calvin-mcd/lumpen/Images/image-1.png

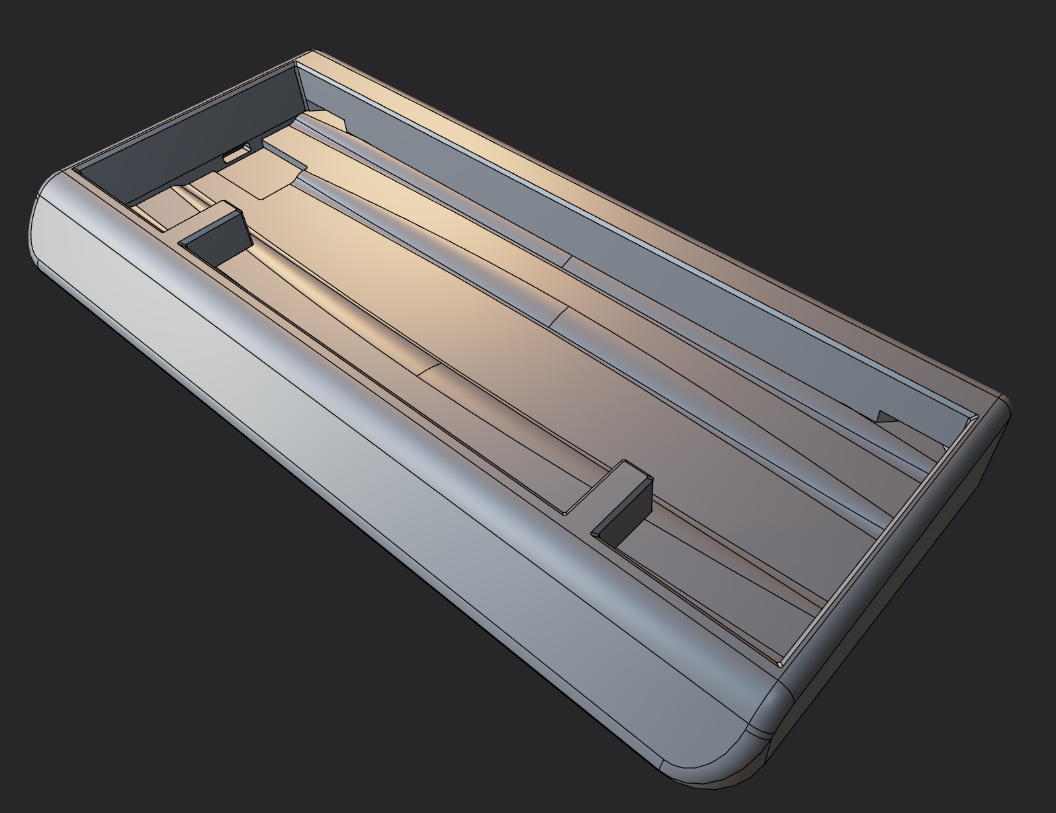
Images/image-1.png
