calvin-mcd/lumpen/Project/lumpen.kicad_sch

## KiCad design Project/lumpen.kicad_sch (2023-02-24)

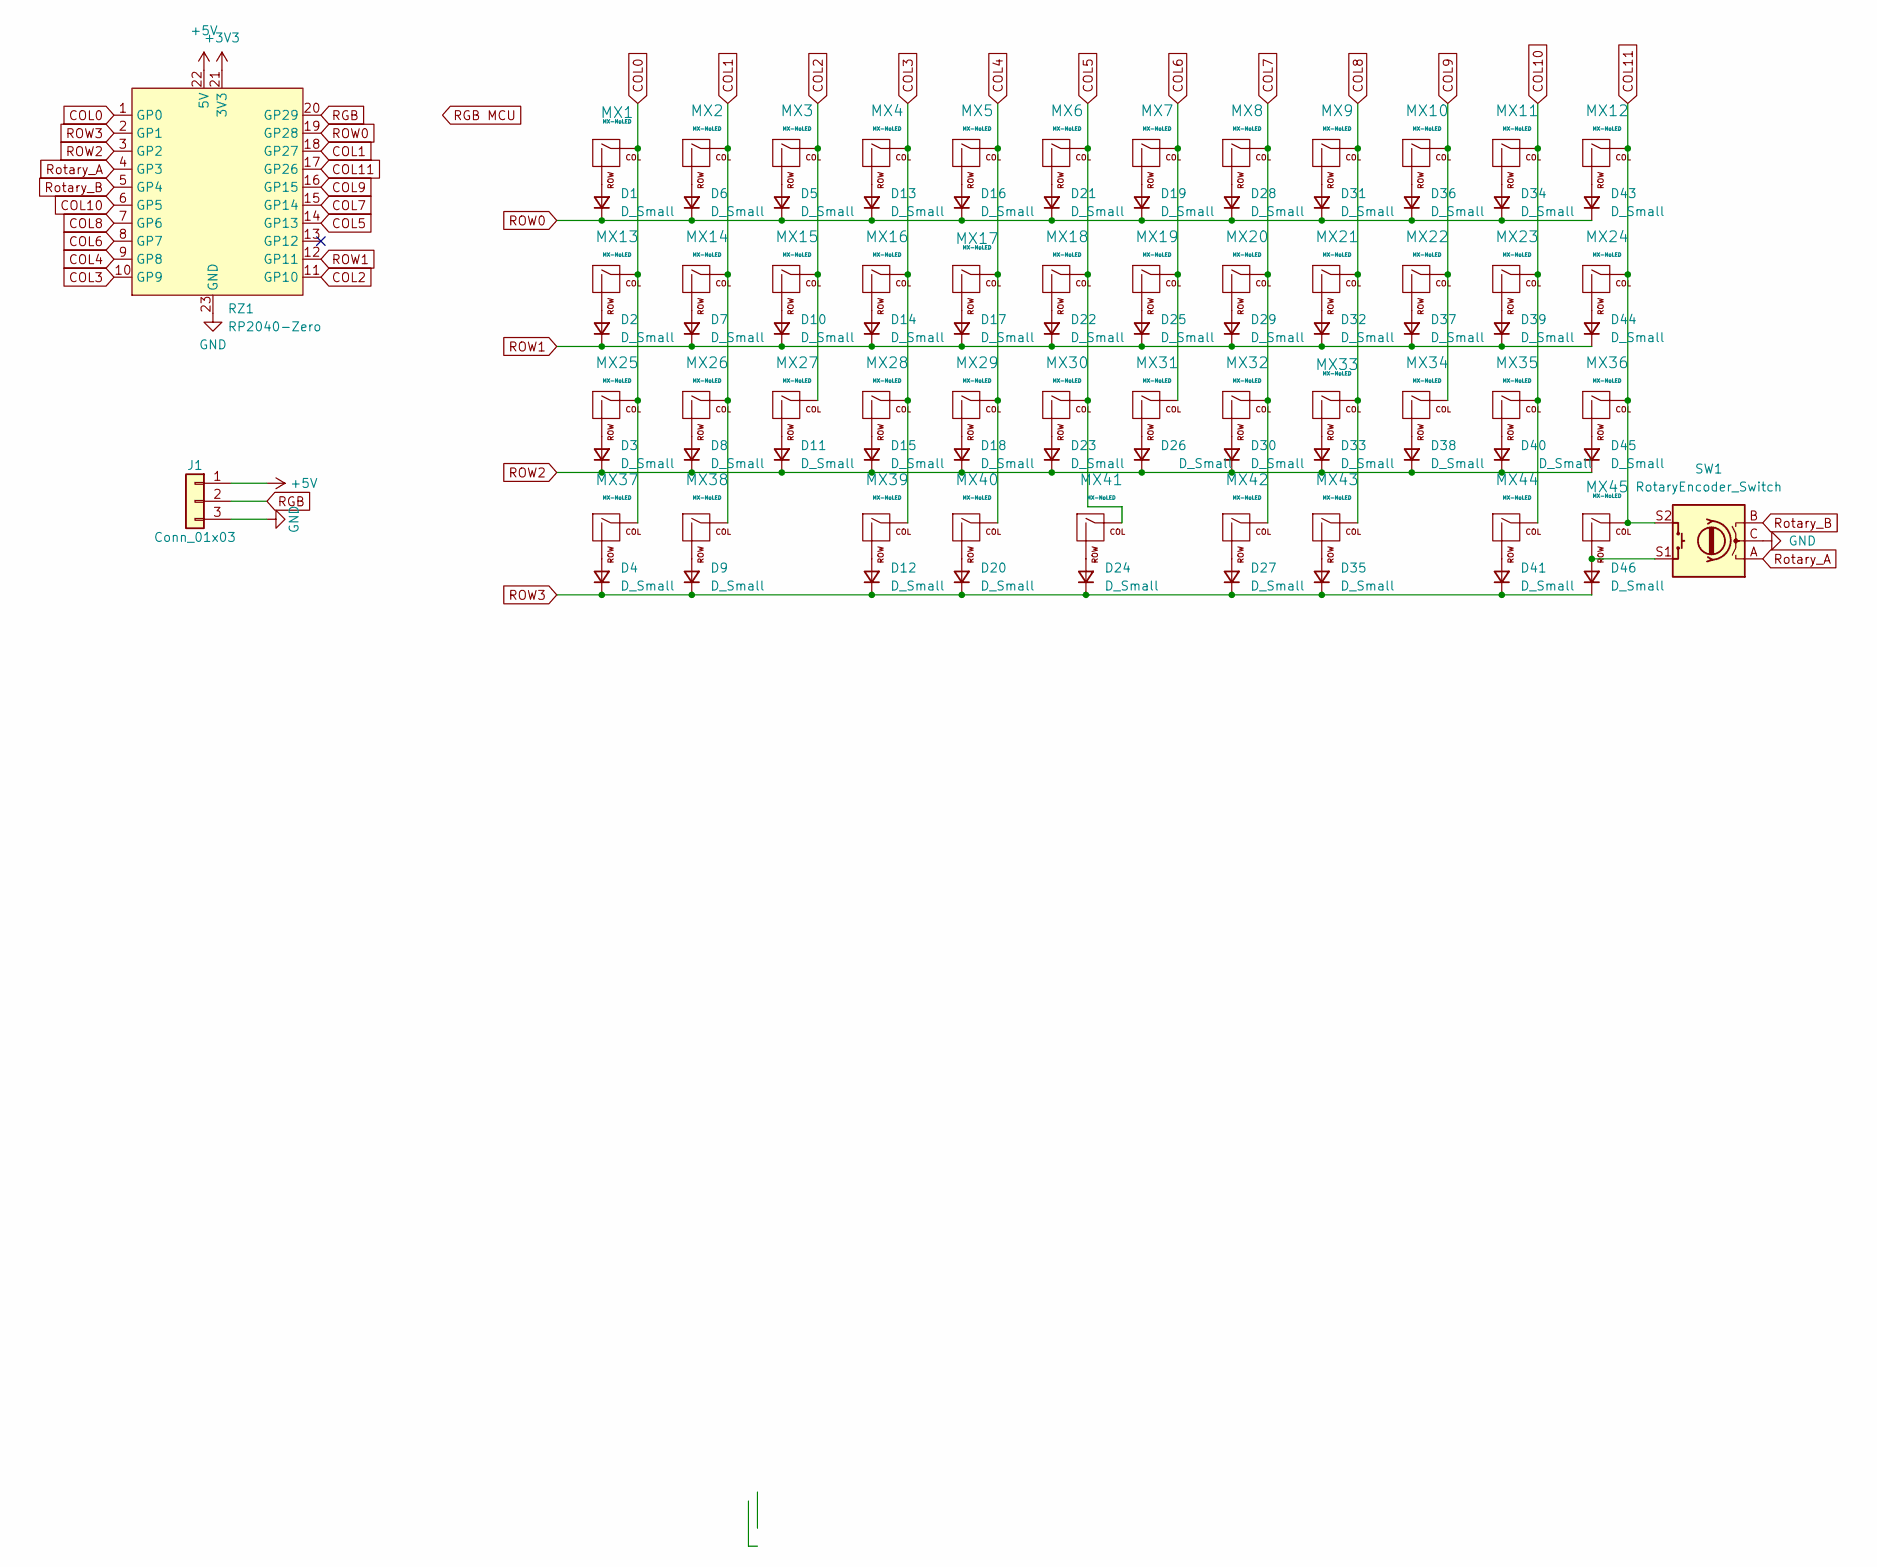
[picture p14: schematic lumpen.kicad_sch]

Parts:
D1, D2, D3, D4, D5, D6, D7, D8, D9, D10, D11, D12, D13, D14, D15, D16, D17, D18, D19, D20, D21, D22, D23, D24, D25, D26, D27, D28, D29, D30, D31, D32, D33, D34, D35, D36, D37, D38, D39, D40, D41, D43, D44, D45, D46: D_Small; Diode-Hybrid-Back
J1: Conn_01x03; PinSocket_1x03_P1.27mm_Vertical
MX1, MX2, MX3, MX4, MX5, MX6, MX7, MX8, MX9, MX10, MX11, MX14, MX15, MX16, MX17, MX18, MX19, MX20, MX21, MX22, MX23, MX26, MX27, MX28, MX29, MX30, MX31, MX32, MX33, MX34, MX35, MX36, MX38, MX39, MX43, MX44: MX-NoLED; MXOnly-1U-NoLED
MX12, MX25: MX-NoLED; MXOnly-1.5U-NoLED
MX13, MX24, MX37, MX45: MX-NoLED; MXOnly-1.25U-NoLED
MX40: MX-NoLED; MXOnly-2.25U-ReversedStabilizers-NoLED
MX41: MX-NoLED; MXOnly-7U-ReversedStabilizers-NoLED
MX42: MX-NoLED; MXOnly-2.75U-ReversedStabilizers-NoLED
RZ1: RP2040-Zero
SW1: RotaryEncoder_Switch; RotaryEncoder_EC11

Connections:
+3V3: RZ1.21 (3V3)
+5V: J1.1, RZ1.22 (5V)
COL0: MX1.1 (COL), MX13.1 (COL), MX25.1 (COL), MX37.1 (COL), RZ1.1 (GP0)
COL1: MX2.1 (COL), MX14.1 (COL), MX26.1 (COL), MX38.1 (COL), RZ1.18 (GP27)
COL2: MX3.1 (COL), MX15.1 (COL), MX27.1 (COL), RZ1.11 (GP10)
COL3: MX4.1 (COL), MX16.1 (COL), MX28.1 (COL), MX39.1 (COL), RZ1.10 (GP9)
COL4: MX5.1 (COL), MX17.1 (COL), MX29.1 (COL), MX40.1 (COL), RZ1.9 (GP8)
COL5: MX6.1 (COL), MX18.1 (COL), MX30.1 (COL), MX41.1 (COL), RZ1.14 (GP13)
COL6: MX7.1 (COL), MX19.1 (COL), MX31.1 (COL), RZ1.8 (GP7)
COL7: MX8.1 (COL), MX20.1 (COL), MX32.1 (COL), MX42.1 (COL), RZ1.15 (GP14)
COL8: MX9.1 (COL), MX21.1 (COL), MX33.1 (COL), MX43.1 (COL), RZ1.7 (GP6)
COL9: MX10.1 (COL), MX22.1 (COL), MX34.1 (COL), RZ1.16 (GP15)
COL10: MX11.1 (COL), MX23.1 (COL), MX35.1 (COL), MX44.1 (COL), RZ1.6 (GP5)
COL11: MX12.1 (COL), MX24.1 (COL), MX36.1 (COL), MX45.1 (COL), RZ1.17 (GP26), SW1.S2
GND: J1.3, RZ1.23 (GND), SW1.C
unnamed: D1.2 (A), MX1.2 (ROW)
unnamed: D2.2 (A), MX13.2 (ROW)
unnamed: D3.2 (A), MX25.2 (ROW)
unnamed: D4.2 (A), MX37.2 (ROW)
unnamed: D5.2 (A), MX3.2 (ROW)
unnamed: D6.2 (A), MX2.2 (ROW)
unnamed: D7.2 (A), MX14.2 (ROW)
unnamed: D8.2 (A), MX26.2 (ROW)
unnamed: D9.2 (A), MX38.2 (ROW)
unnamed: D10.2 (A), MX15.2 (ROW)
unnamed: D11.2 (A), MX27.2 (ROW)
unnamed: D12.2 (A), MX39.2 (ROW)
unnamed: D13.2 (A), MX4.2 (ROW)
unnamed: D14.2 (A), MX16.2 (ROW)
unnamed: D15.2 (A), MX28.2 (ROW)
unnamed: D16.2 (A), MX5.2 (ROW)
unnamed: D17.2 (A), MX17.2 (ROW)
unnamed: D18.2 (A), MX29.2 (ROW)
unnamed: D19.2 (A), MX7.2 (ROW)
unnamed: D20.2 (A), MX40.2 (ROW)
unnamed: D21.2 (A), MX6.2 (ROW)
unnamed: D22.2 (A), MX18.2 (ROW)
unnamed: D23.2 (A), MX30.2 (ROW)
unnamed: D24.2 (A), MX41.2 (ROW)
unnamed: D25.2 (A), MX19.2 (ROW)
unnamed: D26.2 (A), MX31.2 (ROW)
unnamed: D27.2 (A), MX42.2 (ROW)
unnamed: D28.2 (A), MX8.2 (ROW)
unnamed: D29.2 (A), MX20.2 (ROW)
unnamed: D30.2 (A), MX32.2 (ROW)
unnamed: D31.2 (A), MX9.2 (ROW)
unnamed: D32.2 (A), MX21.2 (ROW)
unnamed: D33.2 (A), MX33.2 (ROW)
unnamed: D34.2 (A), MX11.2 (ROW)
unnamed: D35.2 (A), MX43.2 (ROW)
unnamed: D36.2 (A), MX10.2 (ROW)
unnamed: D37.2 (A), MX22.2 (ROW)
unnamed: D38.2 (A), MX34.2 (ROW)
unnamed: D39.2 (A), MX23.2 (ROW)
unnamed: D40.2 (A), MX35.2 (ROW)
unnamed: D41.2 (A), MX44.2 (ROW)
unnamed: D43.2 (A), MX12.2 (ROW)
unnamed: D44.2 (A), MX24.2 (ROW)
unnamed: D45.2 (A), MX36.2 (ROW)
unnamed: D46.2 (A), MX45.2 (ROW), SW1.S1
RGB: J1.2, RZ1.20 (GP29)
ROW0: D1.1 (K), D5.1 (K), D6.1 (K), D13.1 (K), D16.1 (K), D19.1 (K), D21.1 (K), D28.1 (K), D31.1 (K), D34.1 (K), D36.1 (K), D43.1 (K), RZ1.19 (GP28)
ROW1: D2.1 (K), D7.1 (K), D10.1 (K), D14.1 (K), D17.1 (K), D22.1 (K), D25.1 (K), D29.1 (K), D32.1 (K), D37.1 (K), D39.1 (K), D44.1 (K), RZ1.12 (GP11)
ROW2: D3.1 (K), D8.1 (K), D11.1 (K), D15.1 (K), D18.1 (K), D23.1 (K), D26.1 (K), D30.1 (K), D33.1 (K), D38.1 (K), D40.1 (K), D45.1 (K), RZ1.3 (GP2)
ROW3: D4.1 (K), D9.1 (K), D12.1 (K), D20.1 (K), D24.1 (K), D27.1 (K), D35.1 (K), D41.1 (K), D46.1 (K), RZ1.2 (GP1)
Rotary_A: RZ1.4 (GP3), SW1.A
Rotary_B: RZ1.5 (GP4), SW1.B
